jkerdels/RBBA/arduino/RBBA/string_constants.h

#ifndef STRING_CONSTANTS_H
#define STRING_CONSTANTS_H

static const char* str_RBBA        = "RBBA";
static const char* str_v10         = "v1.0";
static const char* str_nPatient    = "new patient";
static const char* str_Calibration = "calibration";
static const char* str_About       = "about";

static const char* str_patient_data = "patient data:";
static const char* str_cm           = "cm";
static const char* str_back         = "back";

static const char* str_calibration   = "calibration:";
static const char* str_motor_encoder = "motor encoder";
static const char* str_bag_volume    = "bag volume";

static const char* str_RBBA_about = "RBBA is open! Cfg:";
static const char* str_comma      = ",";
static const char* str_empty      = "";

static const char* str_max_enc       = "max enc:";
static const char* str_bag_vol_calib = "Bag volume calib.:";
static const char* str_Step          = "Step";
static const char* str_of_nine       = "/9";
static const char* str_go            = "go";
static const char* str_enter_vol     = "Enter vol:";
static const char* str_ml            = "ml";
static const char* str_ok            = "ok";

#endif
